omsi-exhibits/Nakaya_Electronics/docs/Electronics Pictures/IMG_0002.JPG

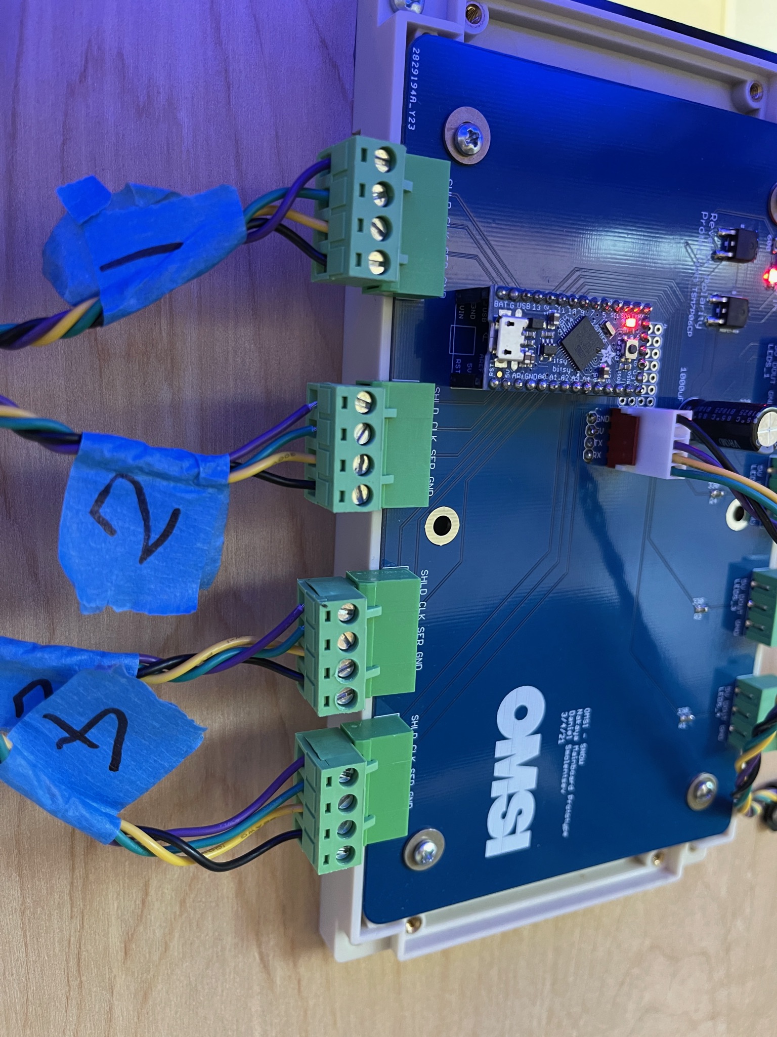
docs/Electronics Pictures/IMG_0002.JPG
