omsi-exhibits/Nakaya_Electronics/docs/Electronics Pictures/IMG_0003.JPG

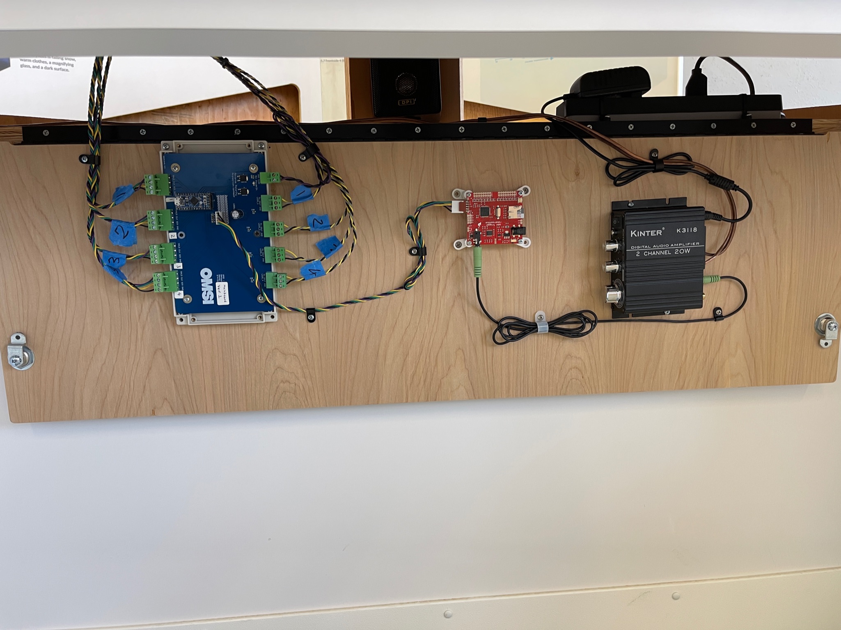
docs/Electronics Pictures/IMG_0003.JPG
