omsi-exhibits/Nakaya_Electronics/docs/Electronics Pictures/IMG_0005.JPG

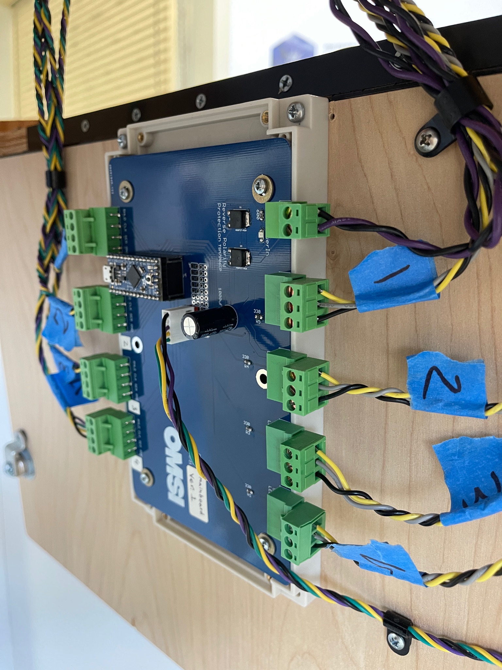
docs/Electronics Pictures/IMG_0005.JPG
