omsi-exhibits/Nakaya_Electronics/docs/Electronics Pictures/IMG_0007.JPG

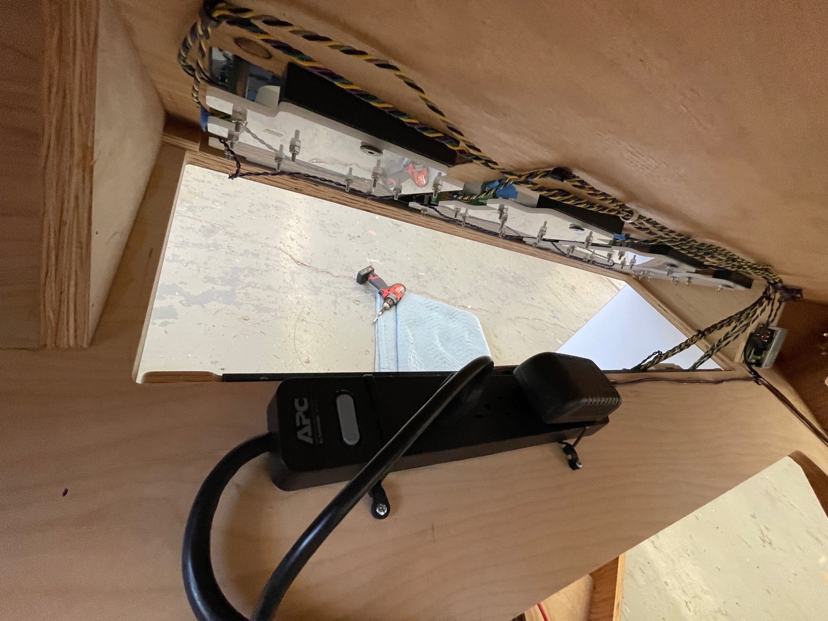
docs/Electronics Pictures/IMG_0007.JPG
