omsi-exhibits/Nakaya_Electronics/docs/Electronics Pictures/IMG_0008.JPG

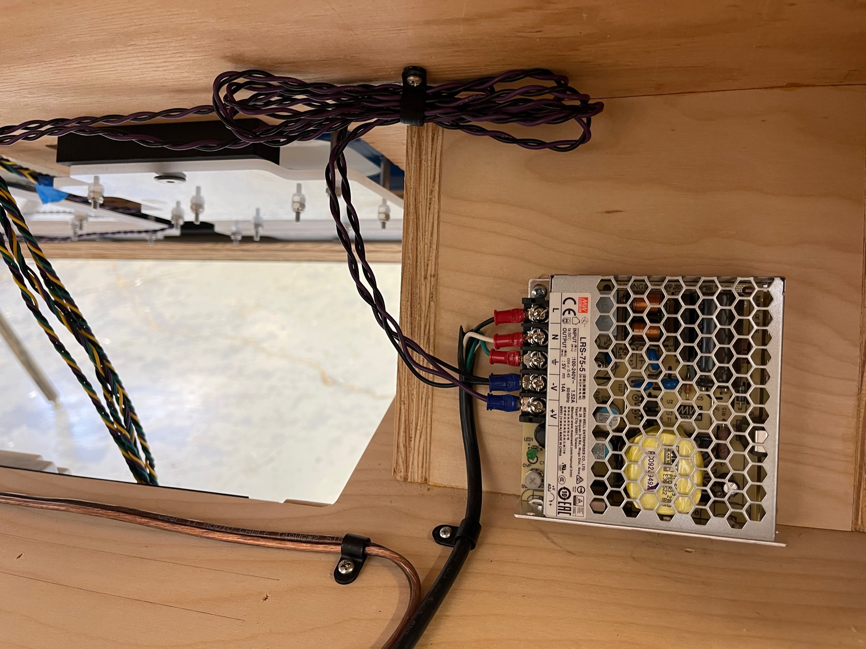
docs/Electronics Pictures/IMG_0008.JPG
