omsi-exhibits/Nakaya_Electronics/docs/Electronics Pictures/IMG_0009.JPG

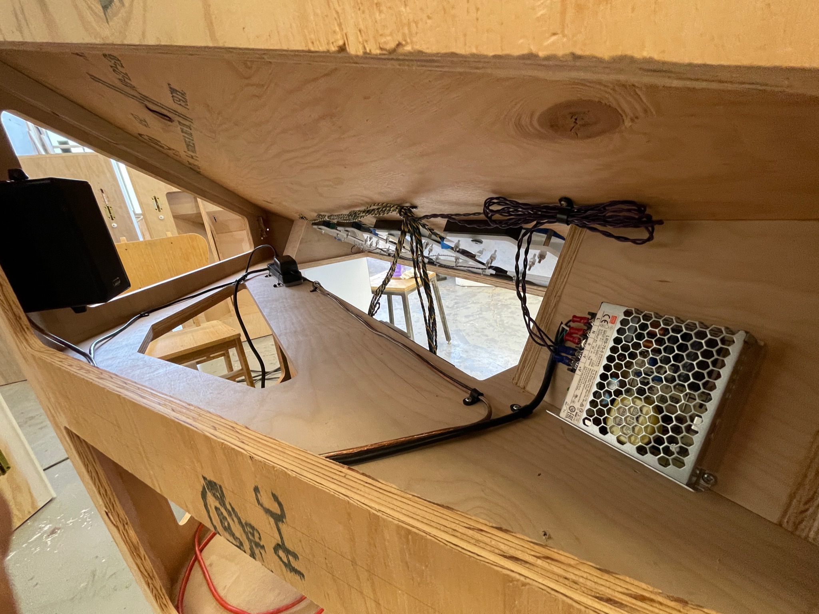
docs/Electronics Pictures/IMG_0009.JPG
