omsi-exhibits/Nakaya_Electronics/docs/Electronics Pictures/IMG_0010.JPG

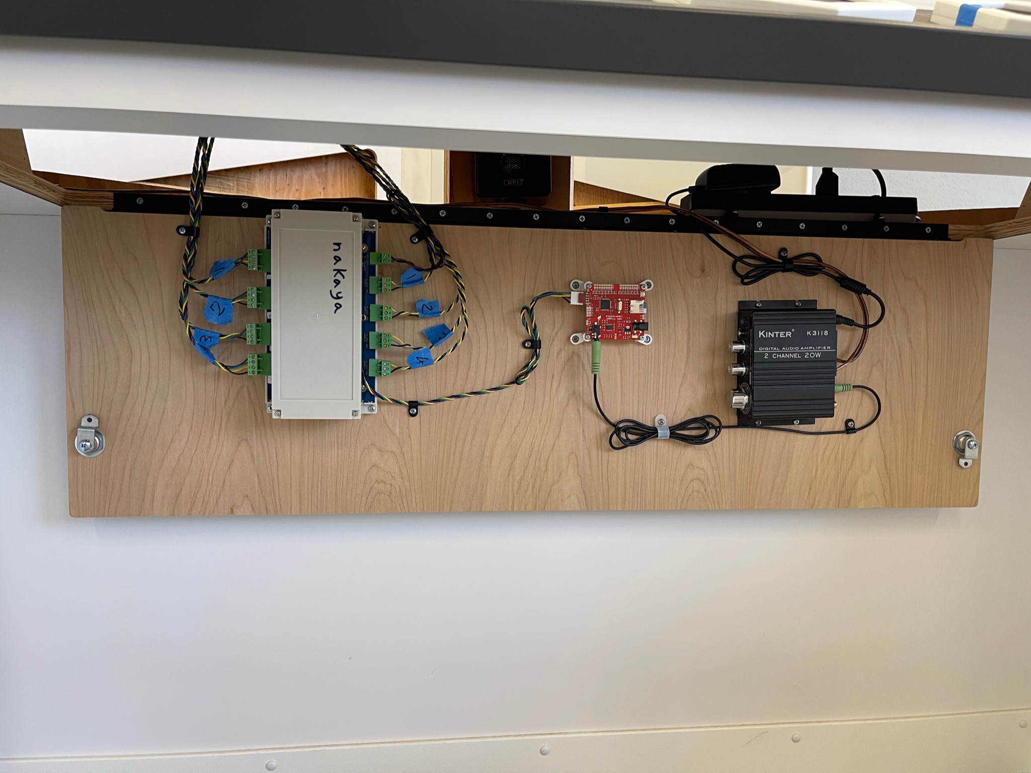
docs/Electronics Pictures/IMG_0010.JPG
