omsi-exhibits/Nakaya_Electronics/docs/Electronics Pictures/IMG_0011.JPG

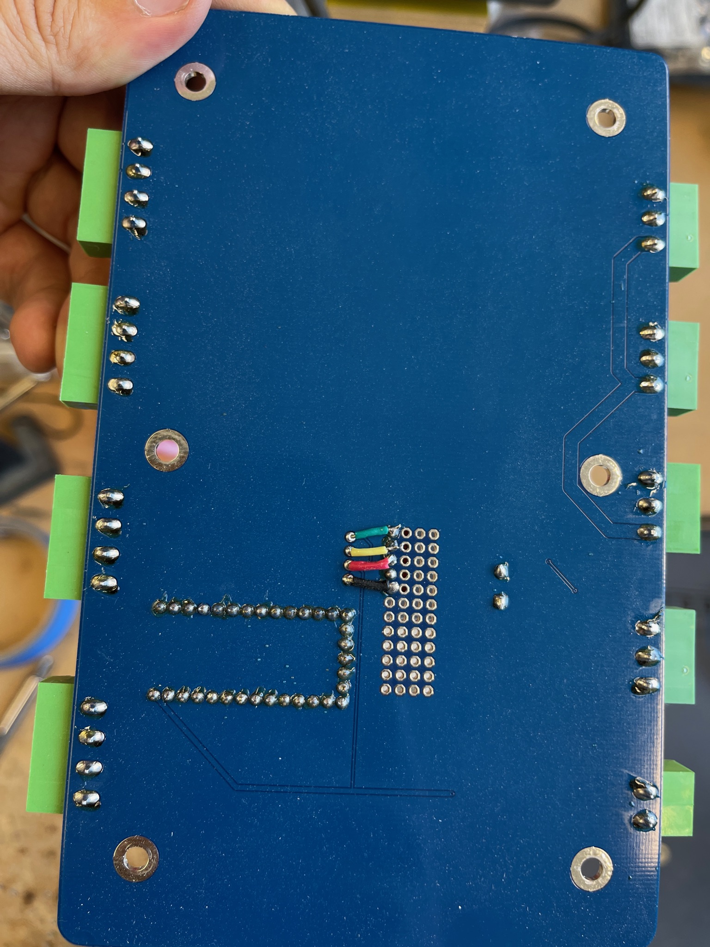
docs/Electronics Pictures/IMG_0011.JPG
