omsi-exhibits/Nakaya_Electronics/docs/Electronics Pictures/IMG_0012.JPG

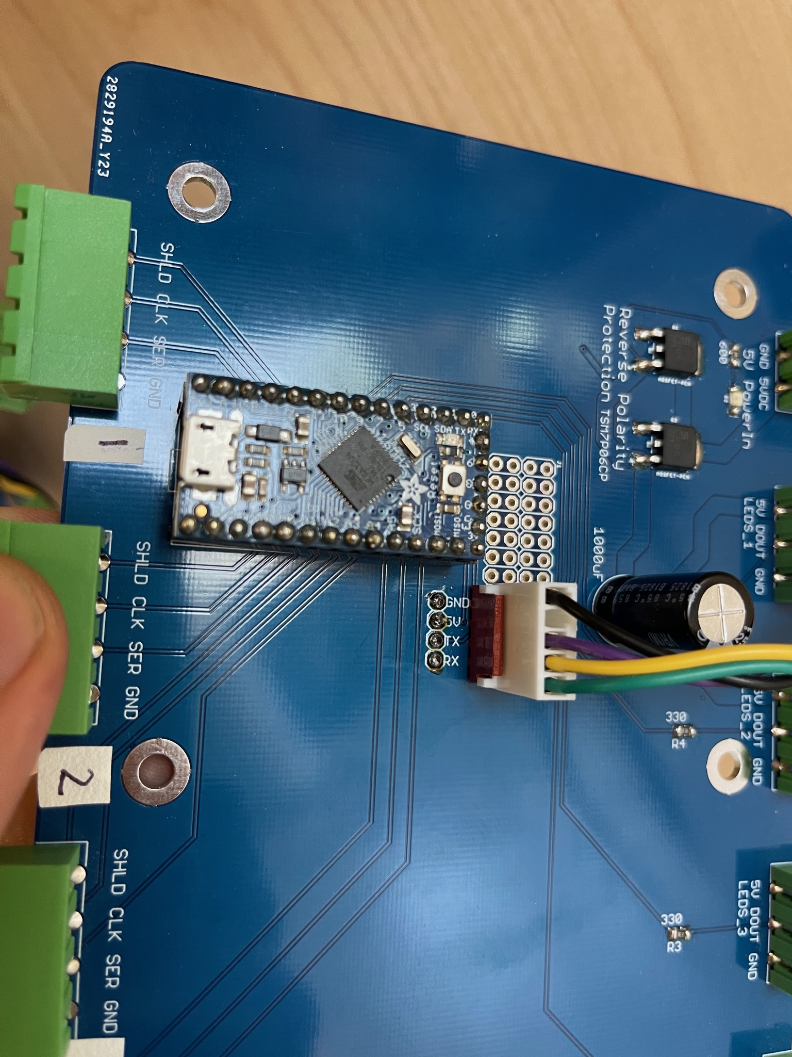
docs/Electronics Pictures/IMG_0012.JPG
