omsi-exhibits/Nakaya_Electronics/docs/Electronics Pictures/IMG_0013.JPG

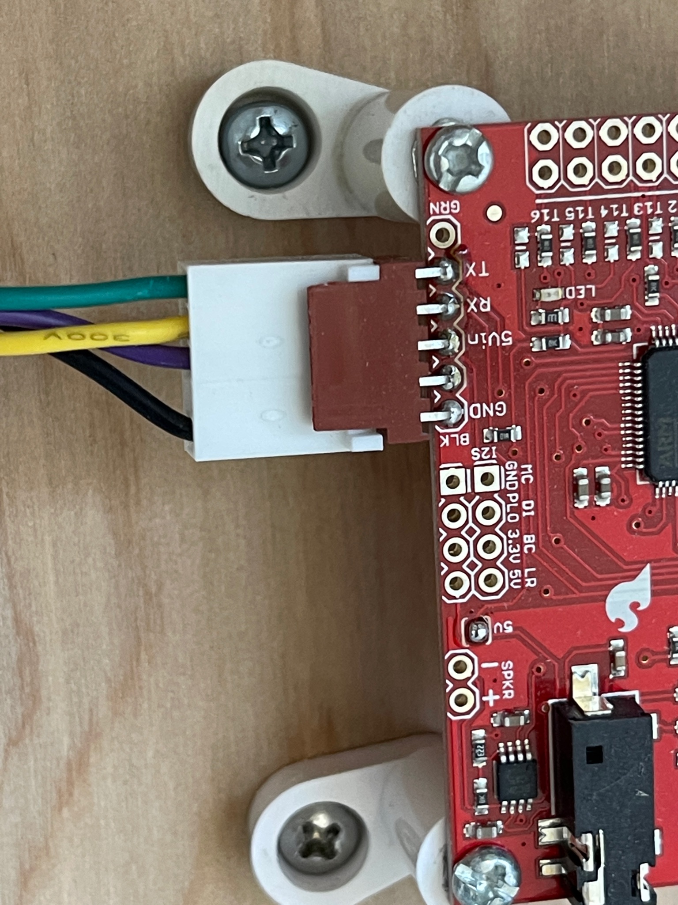
docs/Electronics Pictures/IMG_0013.JPG
