omsi-exhibits/Nakaya_Electronics/docs/Electronics Pictures/IMG_0015.JPG

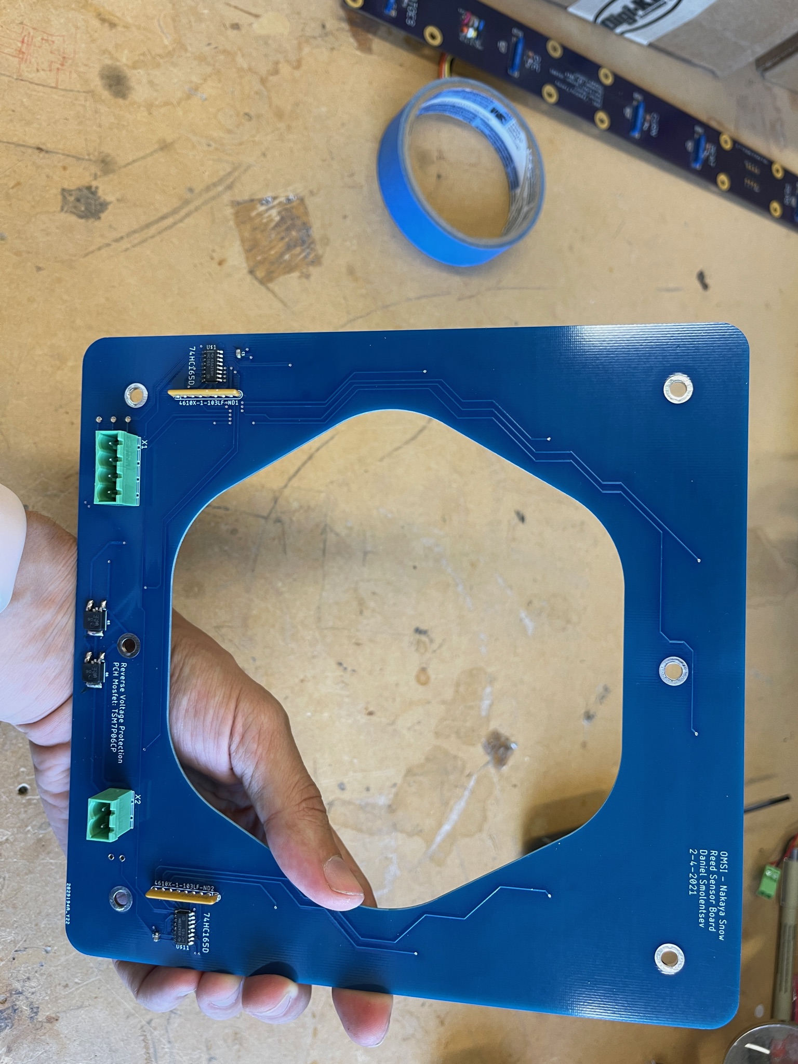
docs/Electronics Pictures/IMG_0015.JPG
