omsi-exhibits/Nakaya_Electronics/docs/PCB Renders/Sensor PCB r1.JPG

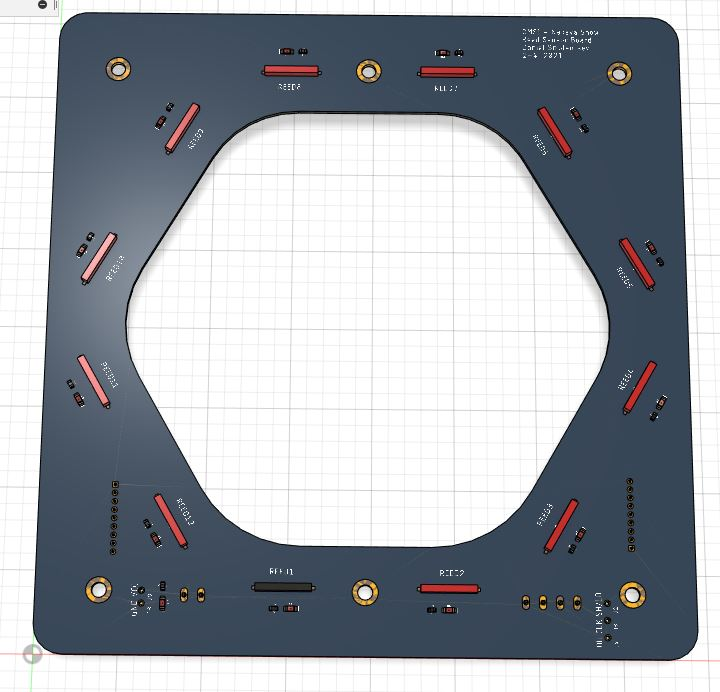
docs/PCB Renders/Sensor PCB r1.JPG
