omsi-exhibits/Nakaya_Electronics/docs/Snow_Flakes Image-to-Magnet Count-8-18-21.jpg

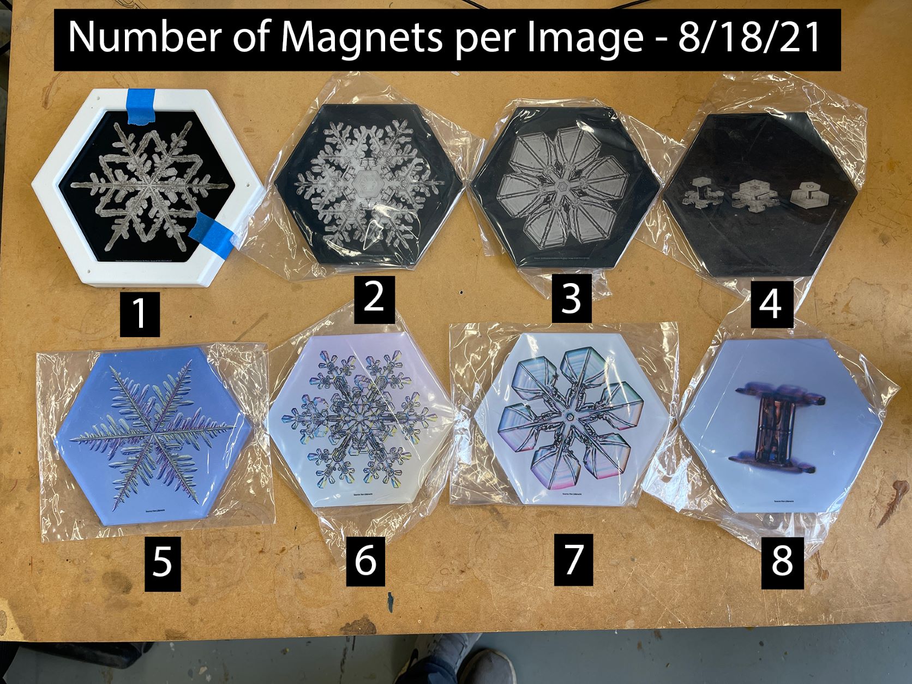
docs/Snow_Flakes Image-to-Magnet Count-8-18-21.jpg
