omsi-exhibits/Nakaya_Electronics/docs/Snow_Flakes Magnet-Placement-Example.jpg

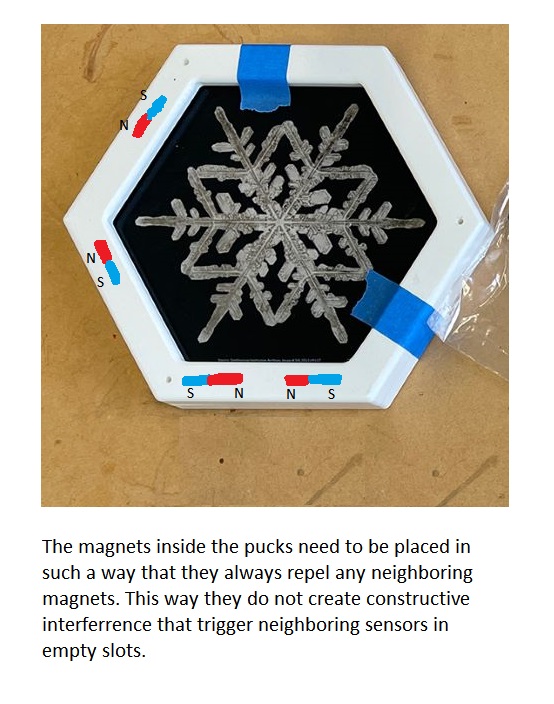
docs/Snow_Flakes Magnet-Placement-Example.jpg
