omsi-exhibits/Nakaya_Electronics/docs/System_Diagram.drawio.png

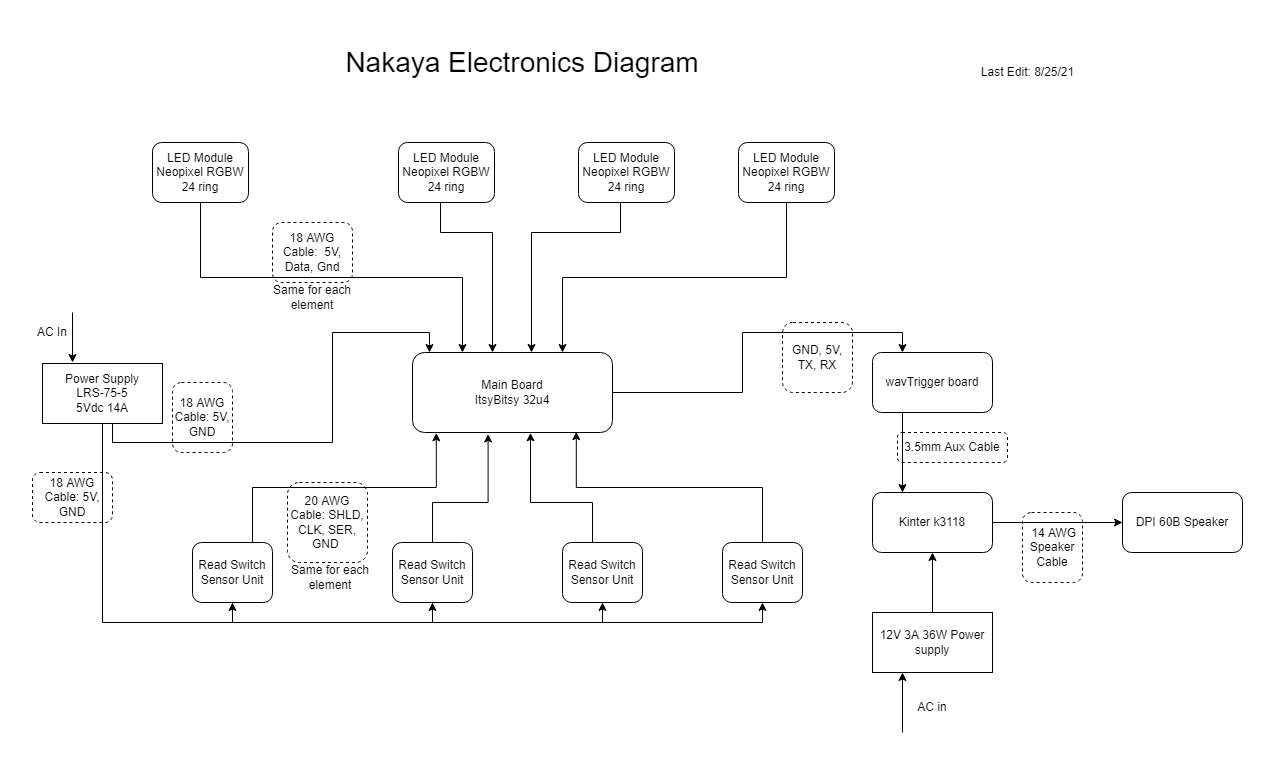
docs/System_Diagram.drawio.png
