omsi-exhibits/Nakaya_Electronics/src/LedModule.cpp

#include "LedModule.h"
#include <Adafruit_NeoPixel.h>
//#include <Arduino.h>

//Uncomment to enable serial debug messages
//#define DEBUG

LedModule::LedModule(uint8_t pin, uint8_t numLeds) {
    mPin = pin;
    mNumLeds = numLeds;
    mTimer = 0;
    mState = IDLE;
    mCount = 0;
    mStrip = Adafruit_NeoPixel(mNumLeds, mPin, NEO_GRBW + NEO_KHZ800);
    mFadeStartColor = Adafruit_NeoPixel::Color(0,0,0);
    mTargetColor = Adafruit_NeoPixel::Color(0,0,0);
    mCurrentFadeOutDuration = 0;
}
void LedModule::begin() {
    mStrip.begin();
    for(int i = 0; i < mNumLeds; i ++) {
        mStrip.setPixelColor(i, 0,0,0,0);
    }
    mStrip.show();
}
uint8_t LedModule::lerpSingle(uint8_t startColor, uint8_t endColor, float deltaTime) {
    // lerp a single color channel. For example R for RGB.
    // deltaTime needs to be normalized value: 0-1
    uint8_t currentColor = 0;
    if(deltaTime <= 1 && deltaTime >= 0) {
        currentColor = (uint8_t) round(lerp(deltaTime, 0.0, 1.0, startColor, endColor));
    } 
    return currentColor;
}
uint32_t LedModule::lerpColor(uint32_t colorStart, uint32_t colorEnd, float deltaTime) {
    // start colors and end colors
    uint8_t u8R = (uint8_t)((colorStart >> 16) & 0xff),
                    u8G = (uint8_t)((colorStart >> 8) & 0xff),
                    u8B = (uint8_t)(colorStart & 0xff);
    uint8_t u8RE = (uint8_t)((colorEnd >> 16) & 0xff),
                    u8GE = (uint8_t)((colorEnd >> 8) & 0xff),
                    u8BE = (uint8_t)(colorEnd & 0xff);
    uint8_t rChan = lerpSingle(u8R, u8RE, deltaTime);
    uint8_t gChan = lerpSingle(u8G, u8GE, deltaTime);
    uint8_t bChan = lerpSingle(u8B, u8BE, deltaTime);
    uint32_t newColor = mStrip.Color(rChan,gChan,bChan,0);
    return newColor;
}

void LedModule::animateSparkle() {
    
}
void LedModule::update() {
    switch(mState) {
        case FADEIN :
            // calculate a fadeIn Brightness 
            if(millis() - mFadeInStartTime < mFadeInDuration) {
                #ifdef DEBUG
                    Serial.print("Fade in duration: ");
                    Serial.println(millis()-mFadeInStartTime);
                #endif
                float deltaTime = ((float)(millis() - mFadeInStartTime)/(float)mFadeInDuration);
                #ifdef DEBUG
                    Serial.print("deltaTime: ");
                    Serial.println(deltaTime);
                #endif
                uint32_t currentFade = lerpColor(0, mTargetColor, deltaTime);
                currentFade = mStrip.gamma32(currentFade);
                mStrip.fill(currentFade);
                mStrip.show();
            } else {
                triggerIdle();
            }
            break;
        case IDLE :
            break;
        case FADEOUT :
            if((millis() - mFadeOutStartTime) < mCurrentFadeOutDuration) {
                // normalized to 0-1
                float deltaTime = ((float)(millis() - mFadeOutStartTime)/(float)mCurrentFadeOutDuration);
                uint32_t currentFade = lerpColor(mFadeStartColor, 0, deltaTime);
                //currentFade = mStrip.gamma32(currentFade); // causes brightness to drop
                mStrip.fill(currentFade);
                mStrip.show();
            } else {
                // incase the leds still had some light when the timer done
                uint32_t currentFade = mStrip.Color(0,0,0,0);
                mStrip.fill(currentFade);
                mStrip.show();
                triggerIdle();
            }
            break;
        default :
            Serial.println(F("Undefined state in ledModule!"));
            break;
    }
}
void LedModule::triggerIdle() {
    mState = IDLE;
}
void LedModule::triggerFadeOut2() {
    triggerFadeOut1();
}
void LedModule::triggerFadeOut1() {
    // check if fadeIn has not completed and if so progress the fadeOut to the right
    // amount so that it Fades out from where the fade in left off.
    mFadeStartColor = mStrip.getPixelColor(0);
    //Serial.print("fadeStart: ");
    if(mState == FADEIN) {
        mCurrentFadeOutDuration = (millis() - mFadeInStartTime);
        #ifdef DEBUG
            Serial.print("Current fade duration: ");
            Serial.println(mCurrentFadeOutDuration);
        #endif
    } else {
        mCurrentFadeOutDuration = mFadeOutDuration;
    }
    mFadeOutStartTime = millis();
    mState = FADEOUT;
}
void LedModule::triggerFadeIn2() {
    mTargetColor = mFadeColor2;
    mFadeInStartTime = millis();
    mState = FADEIN;
}
void LedModule::triggerFadeIn1() {
    // do things on enter fadein state
    // reset fadein details
    mTargetColor = mFadeColor1;
    mFadeInStartTime = millis();
    mState = FADEIN;
}

float LedModule::lerp (float x, float x0, float x1, float y0, float y1) {
    // linear interpellation
    x = x > x1 ? x1 : x;
    x = x < x0 ? x0 : x;
    return y0 + (y1-y0) * ((x-x0)/(x1-x0));
}
