omsi-exhibits/Nakaya_Electronics/src/hw.h

#ifndef HW_H
#define HW_H

#define SER1 14
#define CLK1 16
#define SHLD1 15

#define SER2 A5
#define CLK2 A4
#define SHLD2 A3

#define SER3 A2
#define CLK3 A1
#define SHLD3 A0

#define SER4 12
#define CLK4 11
#define SHLD4 10

#define LEDPIN1 9
#define LEDPIN2 7
#define LEDPIN3 5
#define LEDPIN4 3
#define NUMLEDS 24

#define HEARTLED 13

#endif
